friction07/corne-xiao/rev2/PCB/mx-corne-xiao.kicad_sch

## KiCad design rev2/PCB/mx-corne-xiao.kicad_sch (2024-09-09)

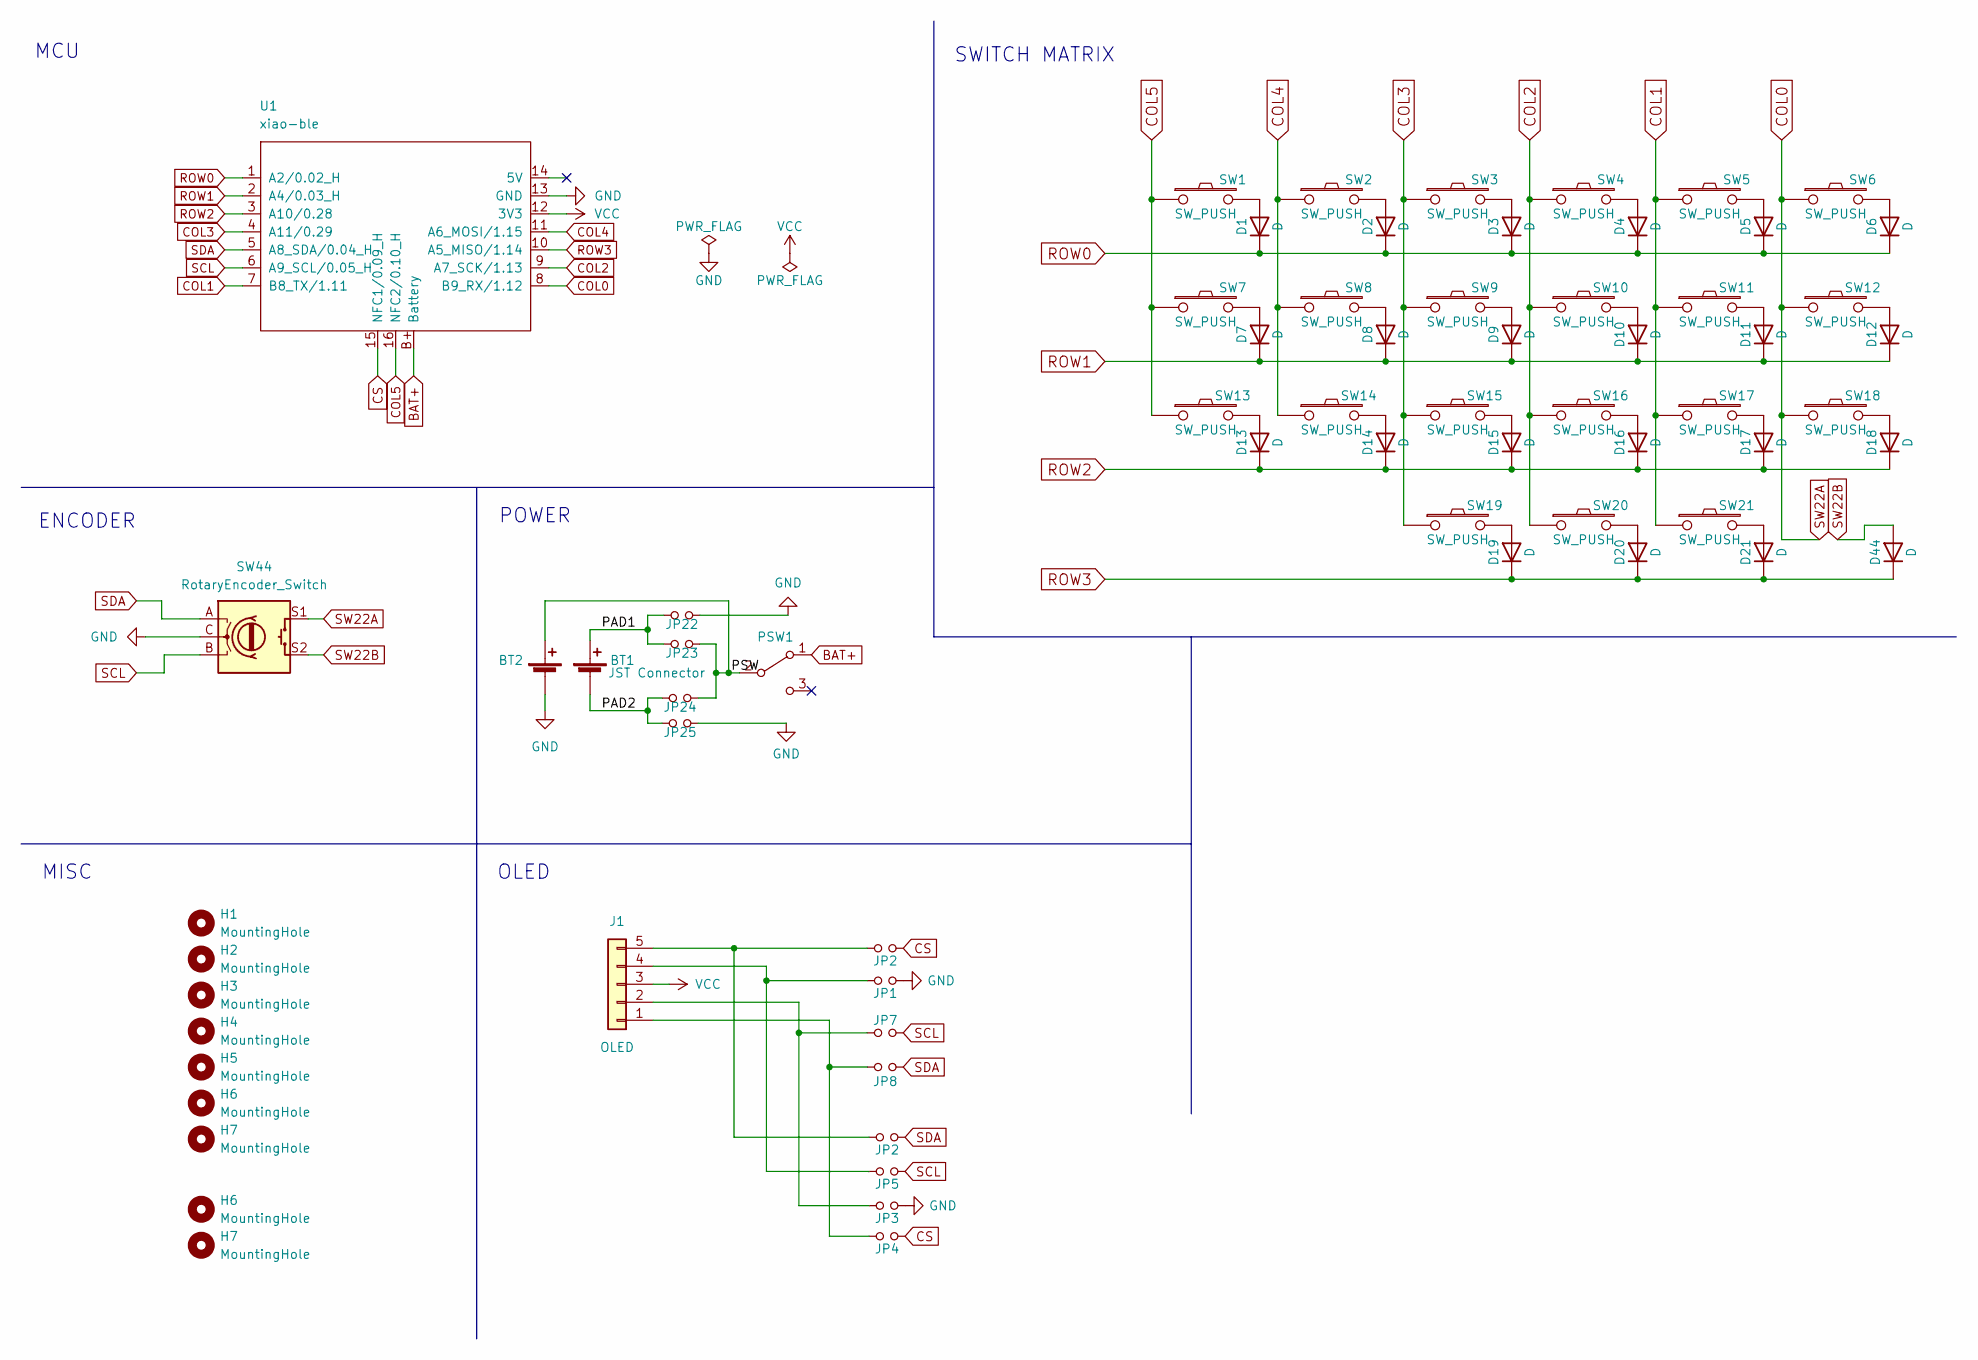
[picture p4: schematic mx-corne-xiao.kicad_sch]

Parts:
BT1: JST Connector; JST_PH_reversible
BT2: Battery_Cell; custombatteryconnector_small
D1, D2, D3, D4, D5, D6, D7, D8, D9, D10, D11, D12, D13, D14, D15, D16, D17, D18, D19, D20, D21, D44: D; Diode_SOD123
H1, H2, H3, H4, H5, H6, H7: MountingHole; M2_HOLE_v2
J1: OLED; nice_view
JP1, JP2, JP3, JP4, JP5, JP7, JP8, JP22, JP23, JP24, JP25: Device_Jumper_NO_Small; Jumper
PSW1: SW_SPDT; MSK12C02_reversible
SW1, SW2, SW3, SW4, SW5, SW6, SW7, SW8, SW9, SW10, SW11, SW12, SW13, SW14, SW15, SW16, SW17, SW18, SW19, SW20: SW_PUSH; cherry_mx_1u
SW21: SW_PUSH; cherry_mx_1.5u
SW44: RotaryEncoder_Switch; RotaryEncoder_Alps_EC11E-Switch_Vertical_H20mm-keebio_modif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
U1: xiao-ble; xiao-rev

Connections:
BAT+: PSW1.1 (A), U1.B+ (Battery)
COL0: SW6.1, SW12.1, SW18.1, SW44.S1, U1.8 (B9_RX/1.12)
COL1: SW5.1, SW11.1, SW17.1, SW21.1, U1.7 (B8_TX/1.11)
COL2: SW4.1, SW10.1, SW16.1, SW20.1, U1.9 (A7_SCK/1.13)
COL3: SW3.1, SW9.1, SW15.1, SW19.1, U1.4 (A11/0.29)
COL4: SW2.1, SW8.1, SW14.1, U1.11 (A6_MOSI/1.15)
COL5: SW1.1, SW7.1, SW13.1, U1.16 (NFC2/0.10_H)
CS: JP2.2, JP4.2, U1.15 (NFC1/0.09_H)
GND: BT2.2 (-), JP1.2, JP3.2, JP22.2, JP25.2, SW44.C, U1.13 (GND)
unnamed: D1.2 (A), SW1.2
unnamed: D2.2 (A), SW2.2
unnamed: D3.2 (A), SW3.2
unnamed: D4.2 (A), SW4.2
unnamed: D5.2 (A), SW5.2
unnamed: D6.2 (A), SW6.2
unnamed: D7.2 (A), SW7.2
unnamed: D8.2 (A), SW8.2
unnamed: D9.2 (A), SW9.2
unnamed: D10.2 (A), SW10.2
unnamed: D11.2 (A), SW11.2
unnamed: D12.2 (A), SW12.2
unnamed: D13.2 (A), SW13.2
unnamed: D14.2 (A), SW14.2
unnamed: D15.2 (A), SW15.2
unnamed: D16.2 (A), SW16.2
unnamed: D17.2 (A), SW17.2
unnamed: D18.2 (A), SW18.2
unnamed: D19.2 (A), SW19.2
unnamed: D20.2 (A), SW20.2
unnamed: D21.2 (A), SW21.2
unnamed: J1.1, JP4.1, JP8.1
unnamed: J1.2, JP3.1, JP7.1
unnamed: J1.4, JP1.1, JP5.1
unnamed: J1.5, JP2.1
PAD1: BT1.1 (+), JP22.1, JP23.1
PAD2: BT1.2 (-), JP24.1, JP25.1
PSW: BT2.1 (+), JP23.2, JP24.2, PSW1.2 (B)
ROW0: D1.1 (K), D2.1 (K), D3.1 (K), D4.1 (K), D5.1 (K), D6.1 (K), U1.1 (A2/0.02_H)
ROW1: D7.1 (K), D8.1 (K), D9.1 (K), D10.1 (K), D11.1 (K), D12.1 (K), U1.2 (A4/0.03_H)
ROW2: D13.1 (K), D14.1 (K), D15.1 (K), D16.1 (K), D17.1 (K), D18.1 (K), U1.3 (A10/0.28)
ROW3: D19.1 (K), D20.1 (K), D21.1 (K), D44.1 (K), U1.10 (A5_MISO/1.14)
SCL: JP5.2, JP7.2, SW44.B, U1.6 (A9_SCL/0.05_H)
SDA: JP2.2, JP8.2, SW44.A, U1.5 (A8_SDA/0.04_H)
SW22B: D44.2 (A), SW44.S2
VCC: J1.3, U1.12 (3V3)

Notes on the sheet:
POWER
ENCODER
MCU
OLED
MISC
SWITCH MATRIX
